wcdnail/TwoTreesSapphirePro/Docs/hints-1/boot.jpg

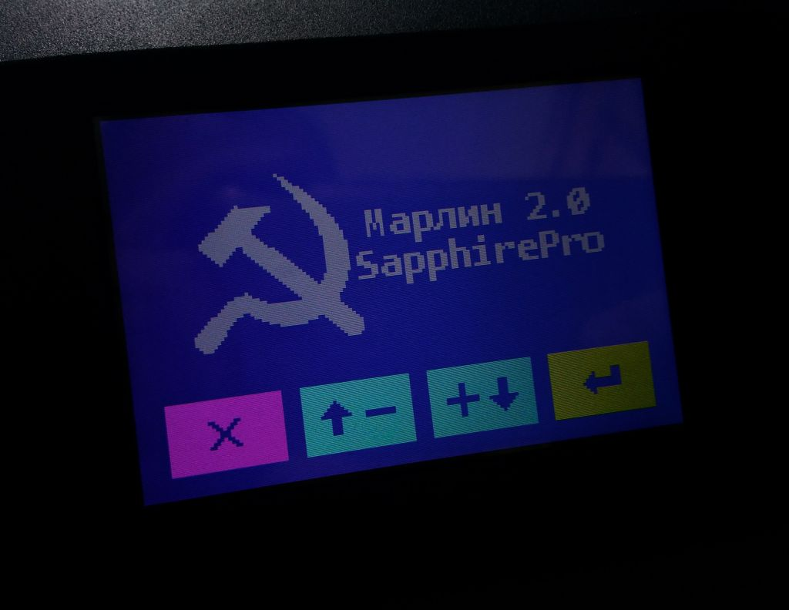
Docs/hints-1/boot.jpg
