wcdnail/TwoTreesSapphirePro/Docs/hints-1/status-panel.jpg

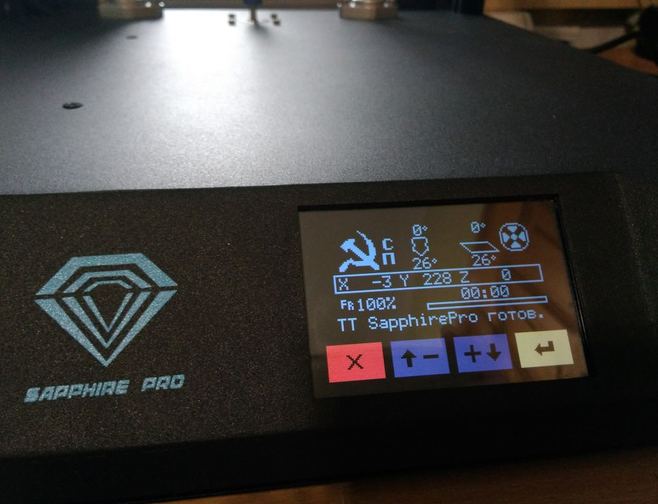
Docs/hints-1/status-panel.jpg
