wcdnail/TwoTreesSapphirePro/Docs/hints-1/status-screen.jpg

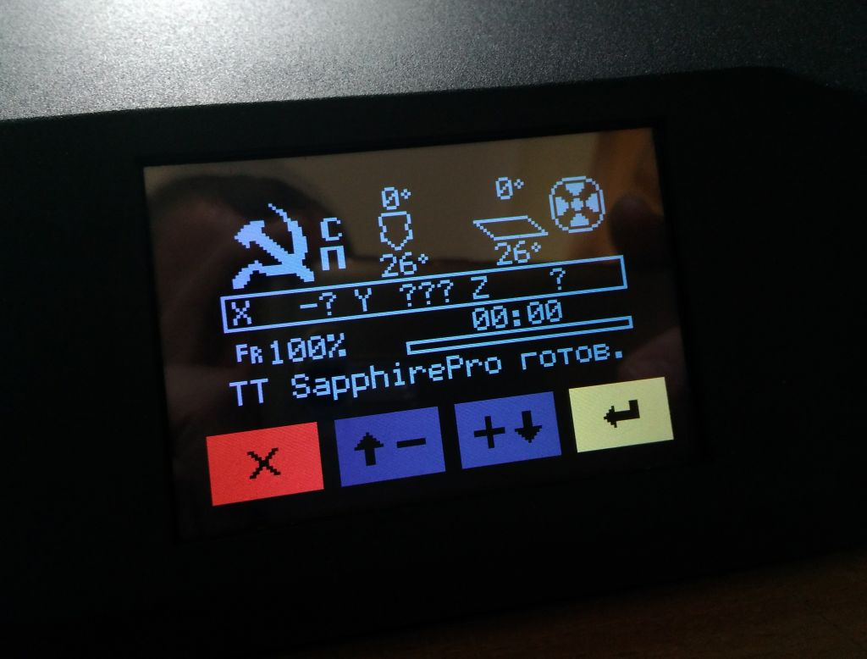
Docs/hints-1/status-screen.jpg
