wcdnail/TwoTreesSapphirePro/Docs/hints-2/1mm-nozzle-e3d-v6-heater-block.jpg

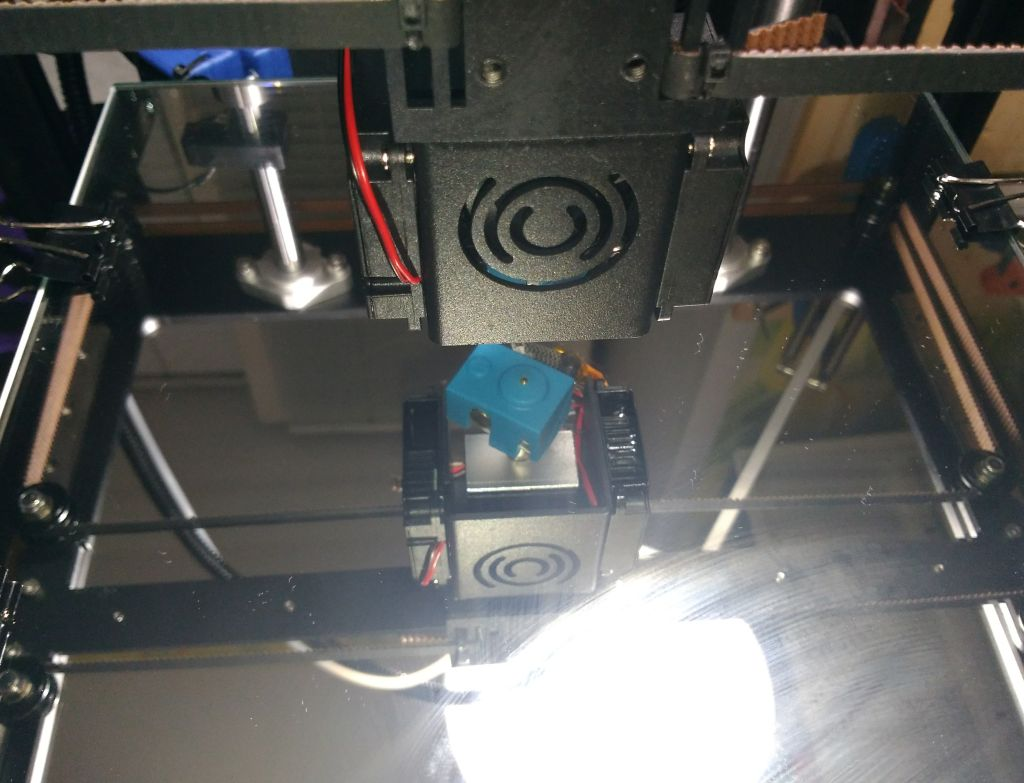
Docs/hints-2/1mm-nozzle-e3d-v6-heater-block.jpg
