wcdnail/TwoTreesSapphirePro/Docs/hints/cura-sapphire-pro-1-quality.png

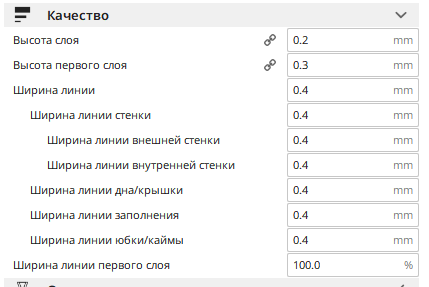
Docs/hints/cura-sapphire-pro-1-quality.png
