wcdnail/TwoTreesSapphirePro/Docs/hints/cura-sapphire-pro-2-perimeter.png

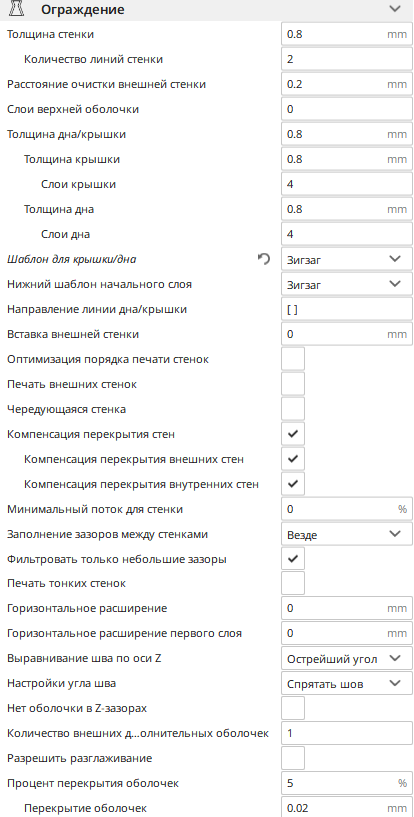
Docs/hints/cura-sapphire-pro-2-perimeter.png
