wcdnail/TwoTreesSapphirePro/Docs/hints/cura-sapphire-pro-3-filling.png

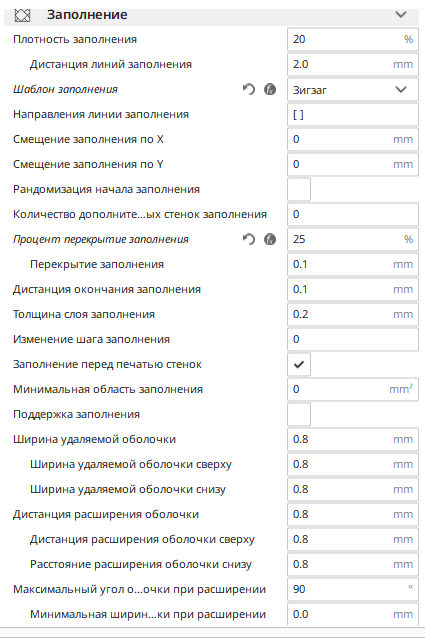
Docs/hints/cura-sapphire-pro-3-filling.png
