wcdnail/TwoTreesSapphirePro/Docs/hints/cura-sapphire-pro-5-speed.png

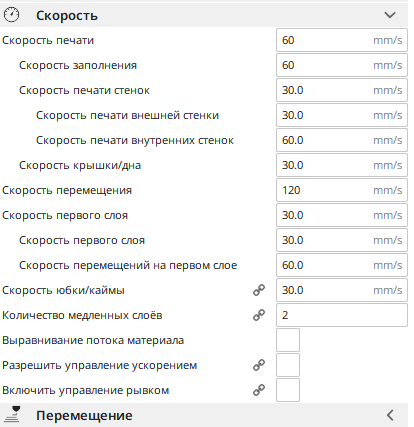
Docs/hints/cura-sapphire-pro-5-speed.png
