wcdnail/TwoTreesSapphirePro/Docs/hints/sapphire-pro-0-marlin-boot1.jpg

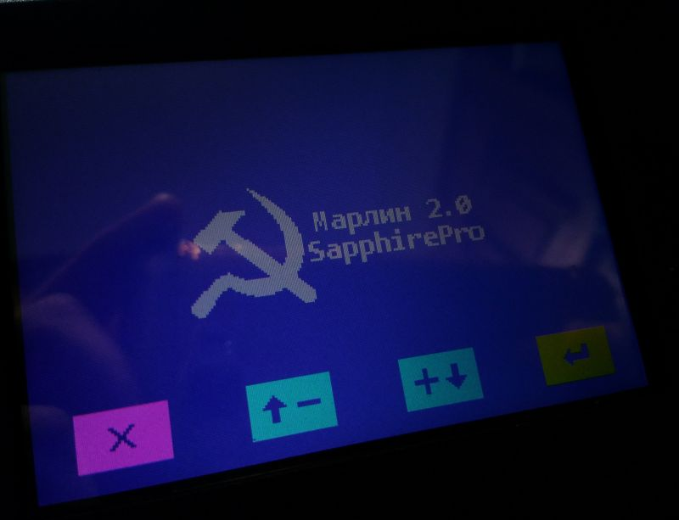
Docs/hints/sapphire-pro-0-marlin-boot1.jpg
