wcdnail/TwoTreesSapphirePro/Docs/hints/sapphire-pro-retract-repetier.png

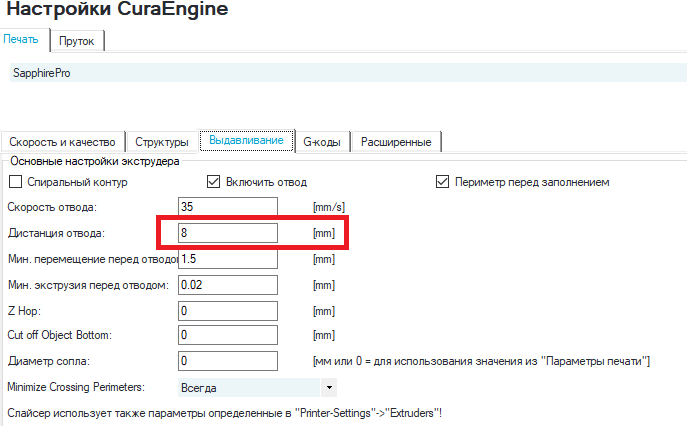
Docs/hints/sapphire-pro-retract-repetier.png
