wcdnail/TwoTreesSapphirePro/Pixmaps/MEL.png

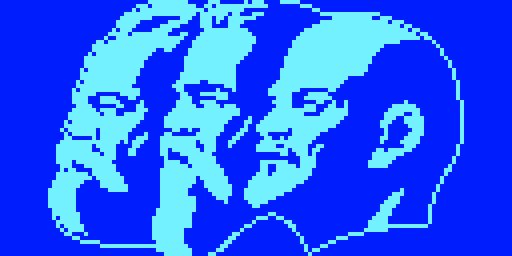
Pixmaps/MEL.png
