wcdnail/TwoTreesSapphirePro/Pixmaps/sapphire-pro-boot-screen.bmp

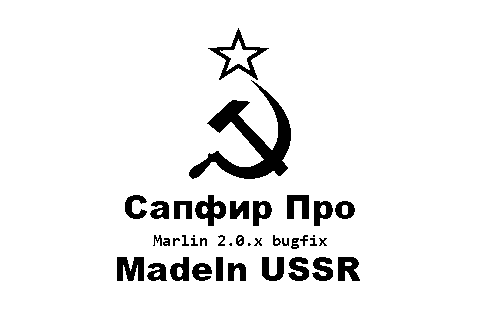
Pixmaps/sapphire-pro-boot-screen.bmp
