wcdnail/TwoTreesSapphirePro/Enhancements/xyz-calibration/100x100-xy-calibrate.stl

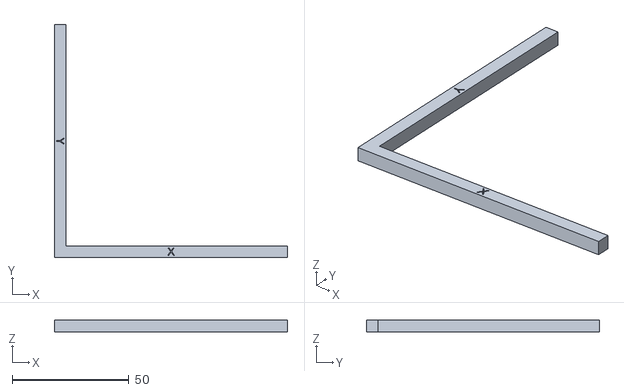
[picture p39: CAD file, 2019-10-07]
Enhancements/xyz-calibration/100x100-xy-calibrate.stl
100.0 x 100.0 x 5.00
