wcdnail/TwoTreesSapphirePro/Enhancements/z-probe/18-Probe-Mount.stl

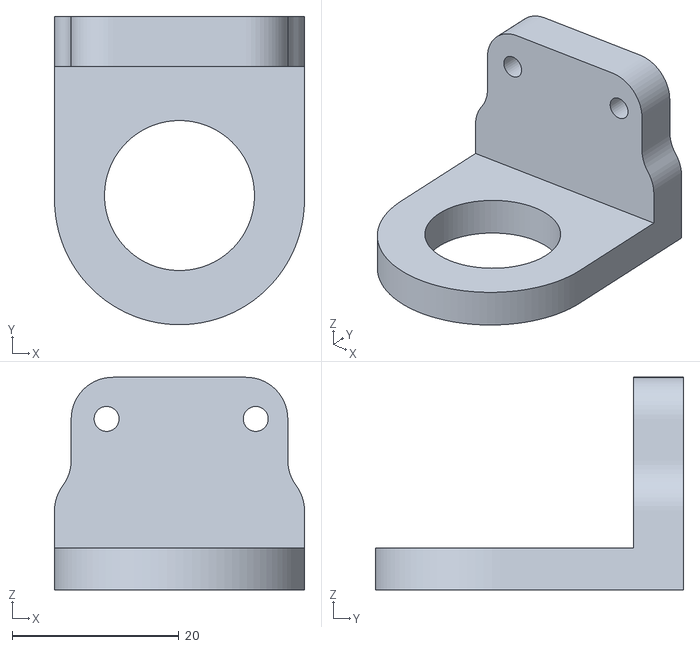
[picture p40: CAD file, 2019-11-04]
Enhancements/z-probe/18-Probe-Mount.stl
30.0 x 37.0 x 25.5
