wcdnail/TwoTreesSapphirePro/Enhancements/3D_CalibrationRuler_v2.stl

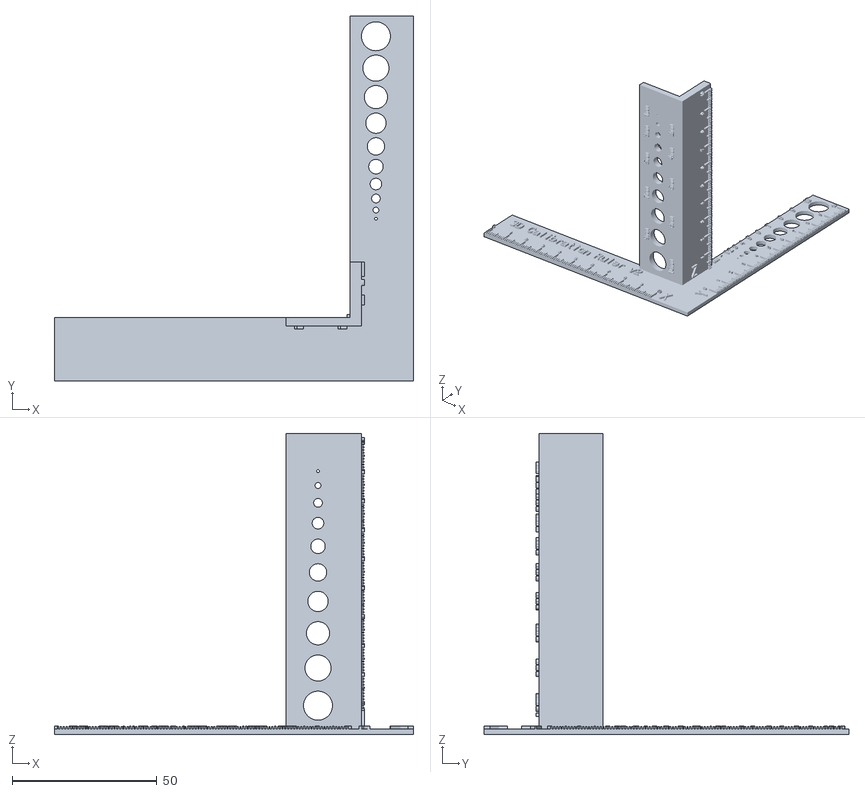
[picture p41: CAD file, 2019-10-07]
Enhancements/3D_CalibrationRuler_v2.stl
124.0 x 126.0 x 104.0
