wcdnail/TwoTreesSapphirePro/Enhancements/bed-clamps-1/bed_clip_1_3mm_glass.stl

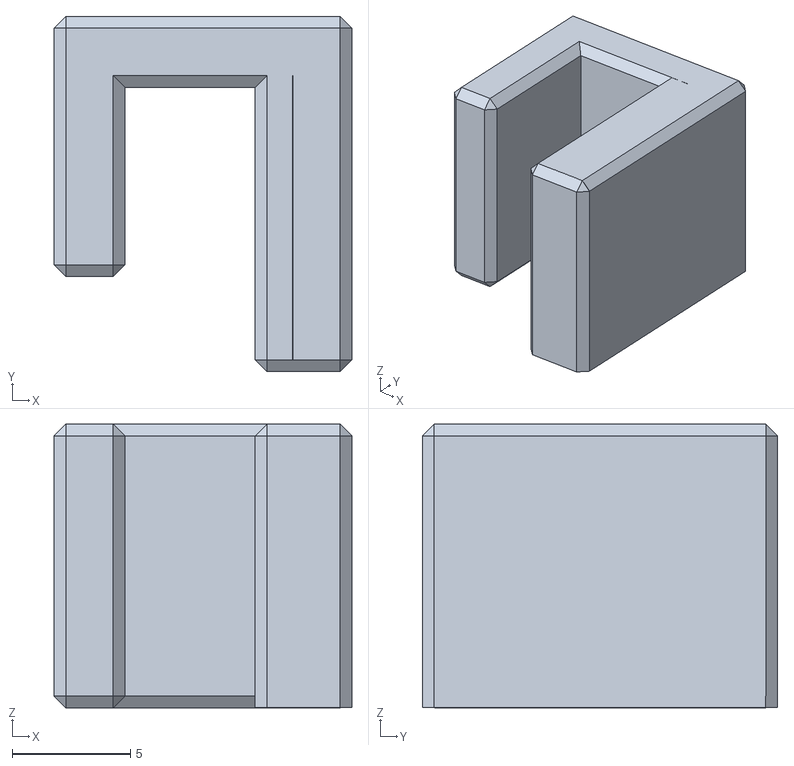
[picture p42: CAD file, 2019-10-05]
Enhancements/bed-clamps-1/bed_clip_1_3mm_glass.stl
12.6 x 15.0 x 12.0
