wcdnail/TwoTreesSapphirePro/Enhancements/bed/Kabelklammer_2.stl

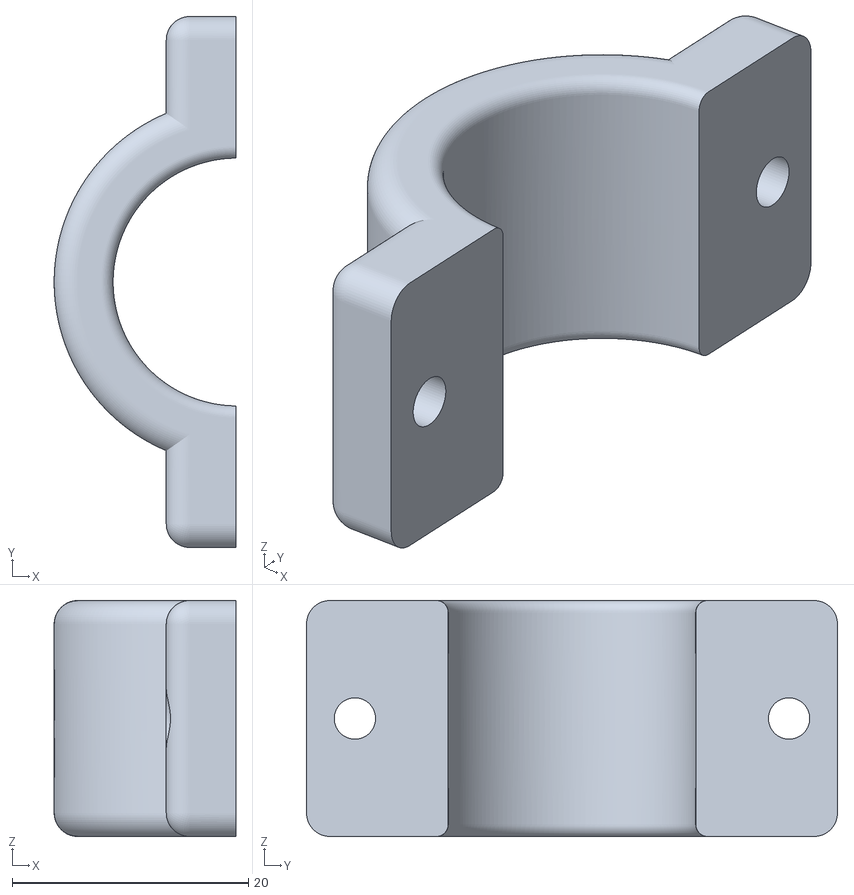
[picture p43: CAD file, 2019-10-05]
Enhancements/bed/Kabelklammer_2.stl
15.4 x 45.0 x 20.0
