wcdnail/TwoTreesSapphirePro/Enhancements/extruder-mount/X_endstop_mount.stl

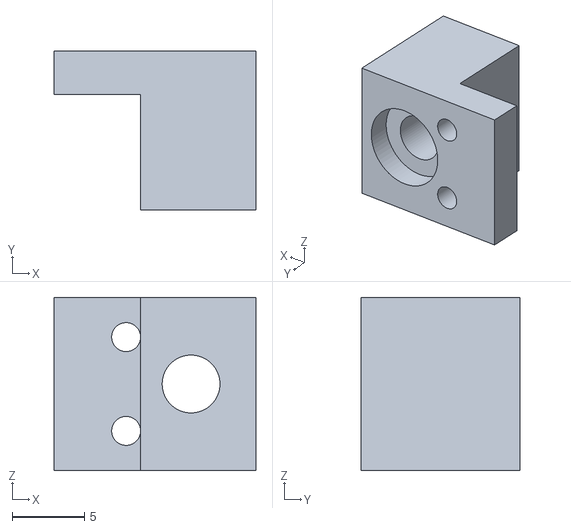
[picture p44: CAD file, 2019-10-07]
Enhancements/extruder-mount/X_endstop_mount.stl
14.0 x 11.0 x 12.0
