wcdnail/TwoTreesSapphirePro/Enhancements/bed-clamps-1/bed_clip_2.stl

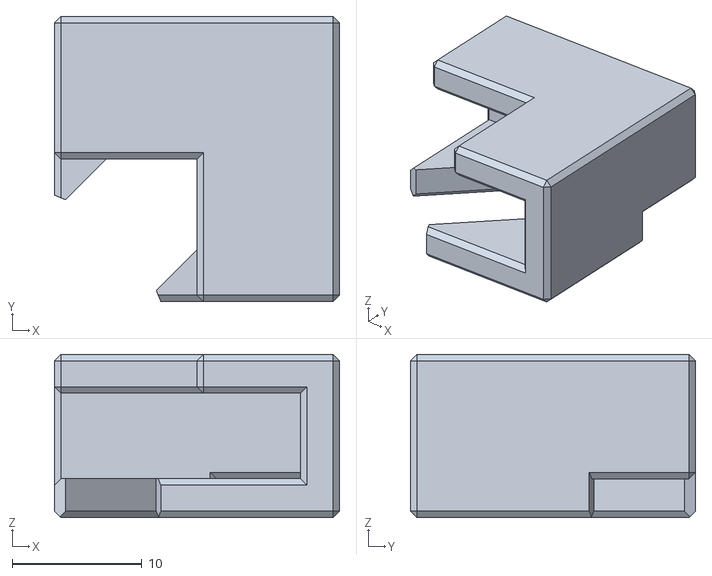
[picture p45: CAD file, 2019-10-05]
Enhancements/bed-clamps-1/bed_clip_2.stl
22.0 x 22.0 x 12.6
