wcdnail/TwoTreesSapphirePro/Enhancements/bed/bed-glass-clamps.stl

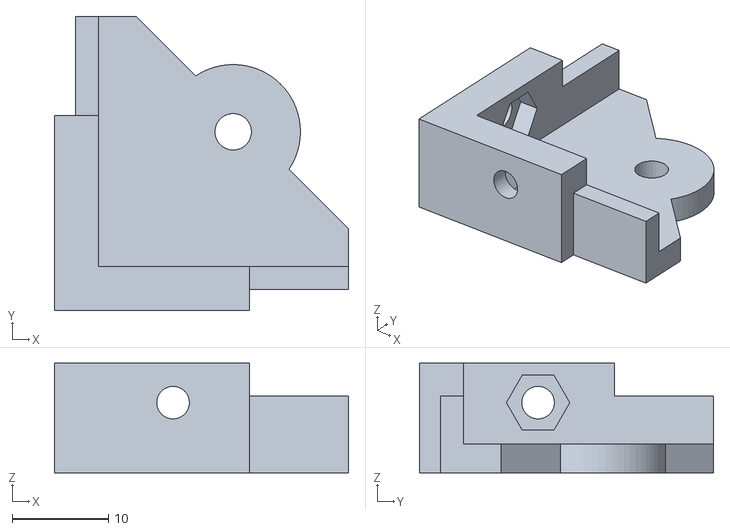
[picture p46: CAD file, 2019-10-05]
Enhancements/bed/bed-glass-clamps.stl
30.6 x 30.6 x 11.4
