wcdnail/TwoTreesSapphirePro/Enhancements/extruder-mount/extruder_mount.stl

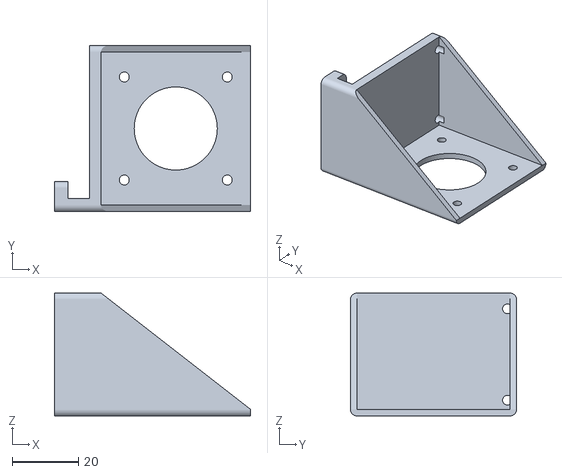
[picture p47: CAD file, 2019-10-07]
Enhancements/extruder-mount/extruder_mount.stl
59.0 x 50.0 x 37.0
