wcdnail/TwoTreesSapphirePro/Enhancements/bed-clamps-1/bed_clip_4.stl

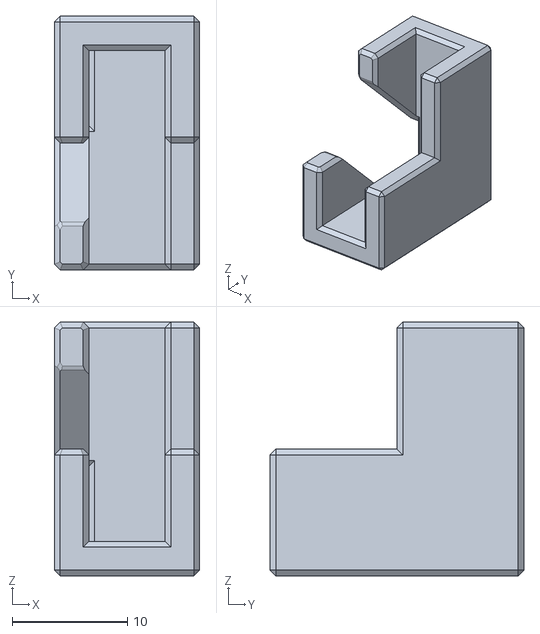
[picture p48: CAD file, 2019-10-05]
Enhancements/bed-clamps-1/bed_clip_4.stl
12.6 x 22.0 x 22.0
