wcdnail/TwoTreesSapphirePro/Enhancements/extruder-mount/stepper_mount.stl

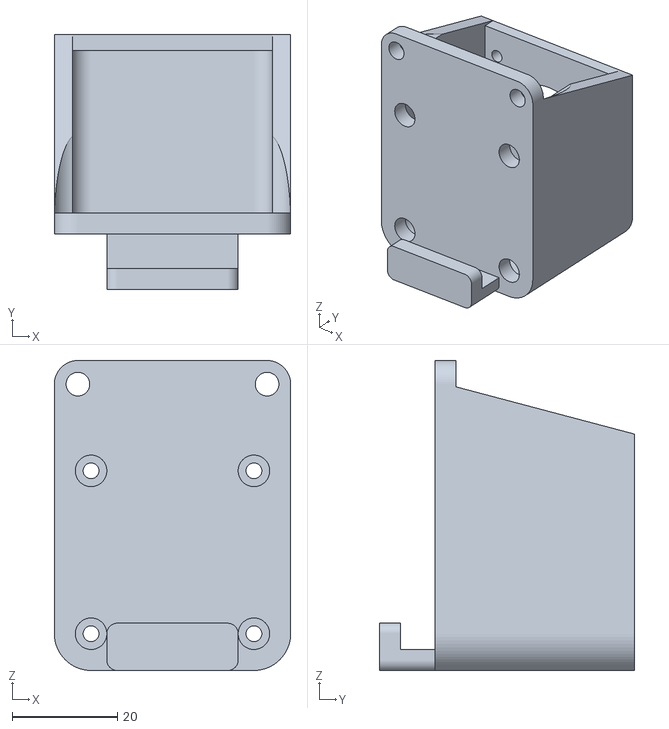
[picture p49: CAD file, 2019-10-07]
Enhancements/extruder-mount/stepper_mount.stl
45.0 x 48.5 x 59.0
