wcdnail/TwoTreesSapphirePro/Enhancements/bed-clamps-1/bed_clip_4_3mm_glass.stl

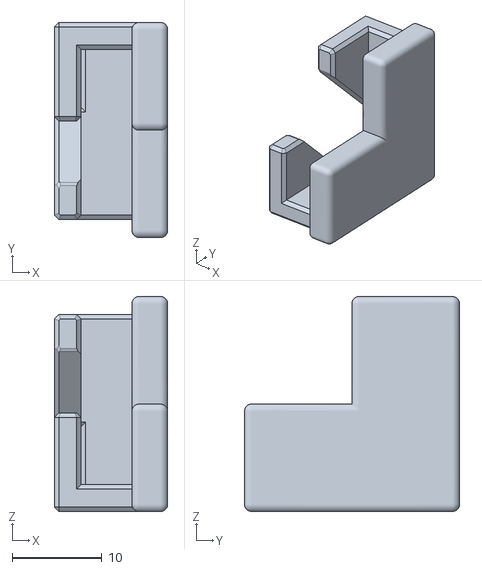
[picture p50: CAD file, 2019-10-05]
Enhancements/bed-clamps-1/bed_clip_4_3mm_glass.stl
12.7 x 24.0 x 24.0
