wcdnail/TwoTreesSapphirePro/Docs/hints/cura-sapphire-pro-0-printer-settings-1.png

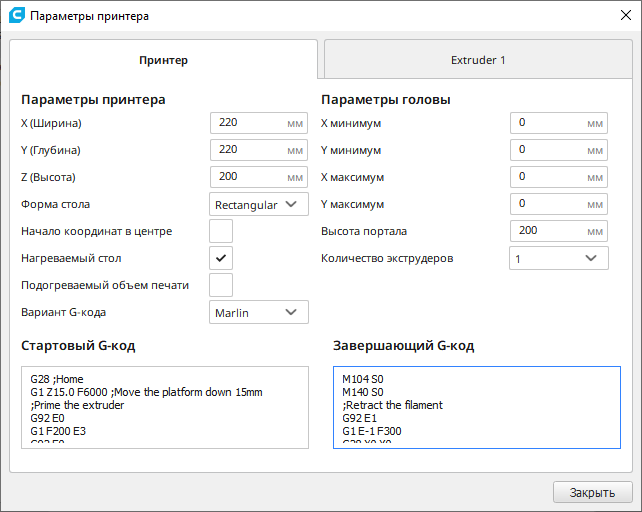
Docs/hints/cura-sapphire-pro-0-printer-settings-1.png
