wcdnail/TwoTreesSapphirePro/Docs/hints/cura-sapphire-pro-0-printer-settings-2.png

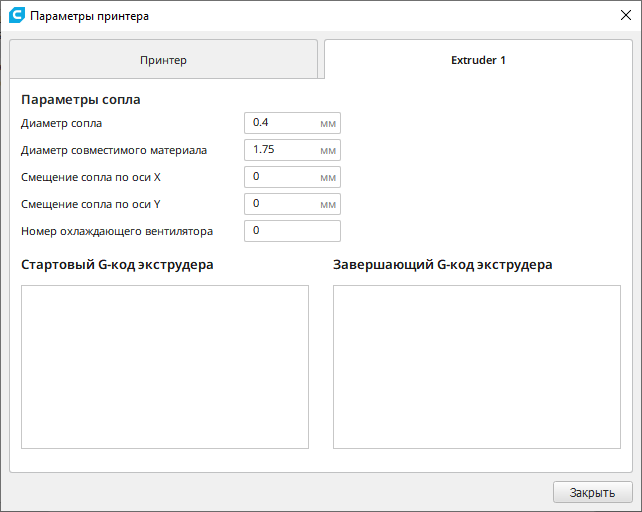
Docs/hints/cura-sapphire-pro-0-printer-settings-2.png
