wcdnail/TwoTreesSapphirePro/Pixmaps/ussr-qa.png

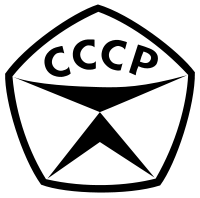
Pixmaps/ussr-qa.png
