wcdnail/TwoTreesSapphirePro/Docs/hints-2/color-debug.jpg

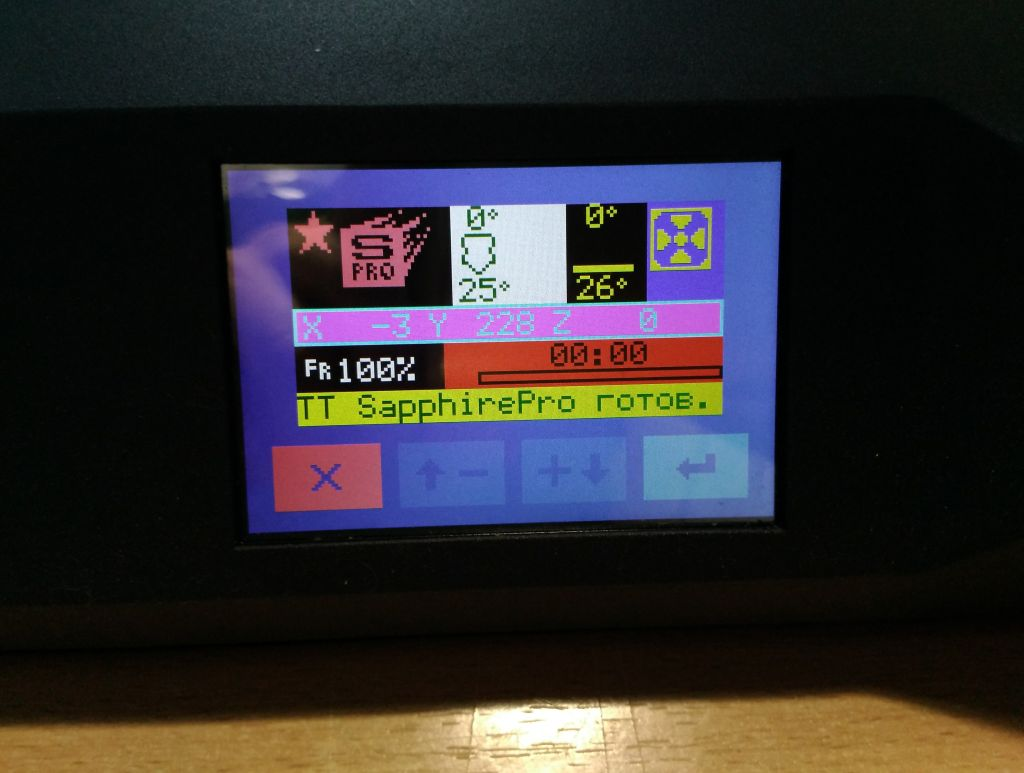
Docs/hints-2/color-debug.jpg
